WannaBAcoder/PCB-Powerwalls/15s4p_PCB/Renders/15s4p_board_bottom.jpg

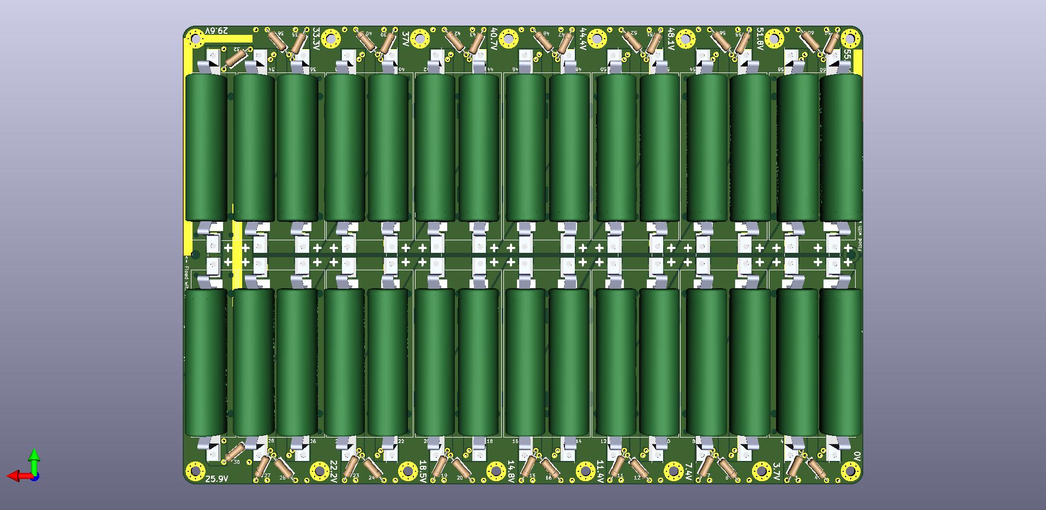
15s4p_PCB/Renders/15s4p_board_bottom.jpg
