WannaBAcoder/PCB-Powerwalls/BMS_display_adapter_PCB/bms.png

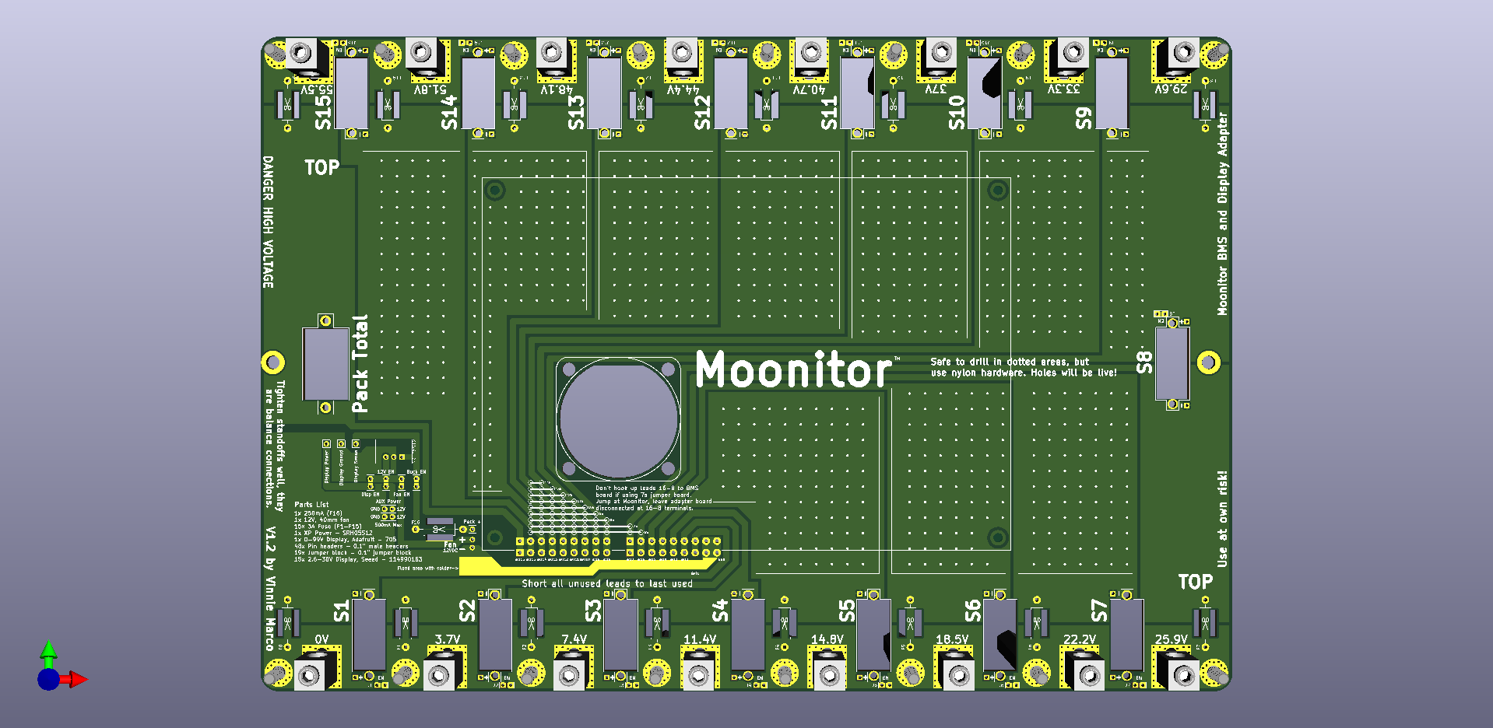
BMS_display_adapter_PCB/bms.png
