WannaBAcoder/PCB-Powerwalls/BMS_display_adapter_PCB/Renderings/bottom.png

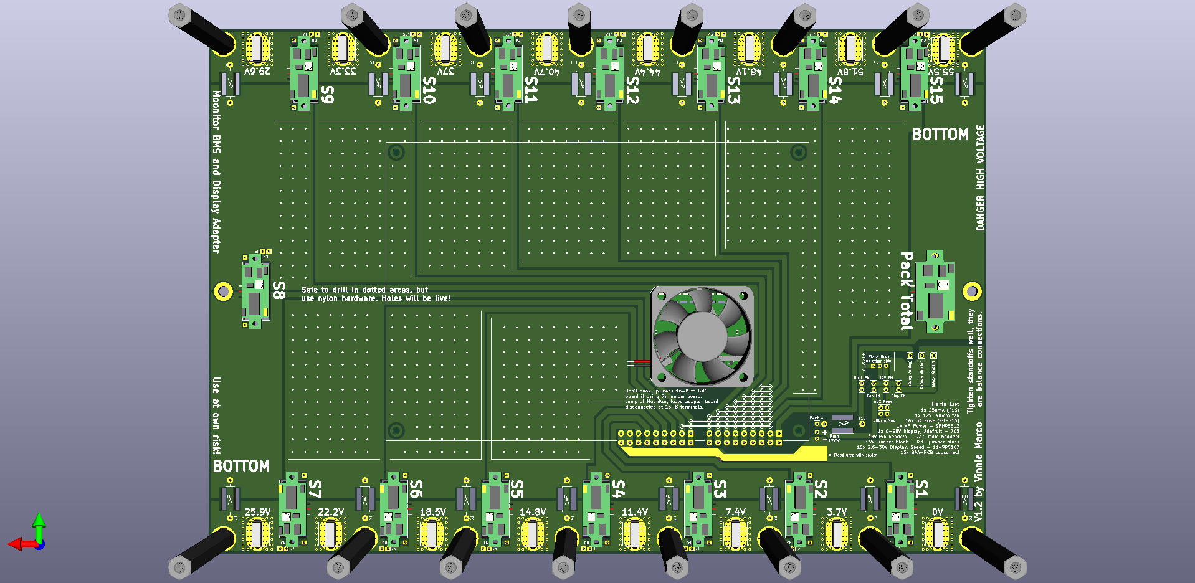
BMS_display_adapter_PCB/Renderings/bottom.png
