WannaBAcoder/PCB-Powerwalls/BMS_display_adapter_PCB/Renderings/side.png

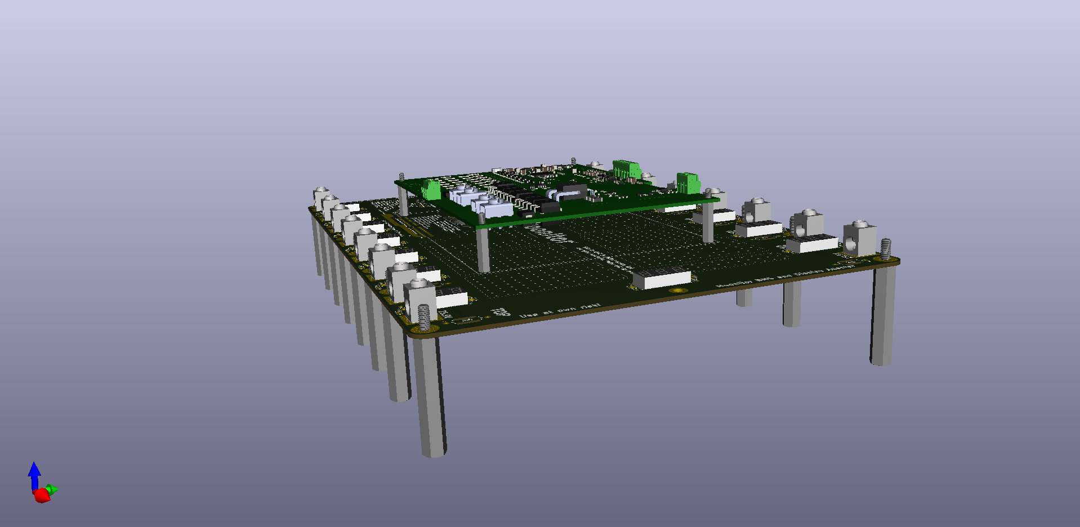
BMS_display_adapter_PCB/Renderings/side.png
